PieroBorgatta/Laveggio-Printomatic/firmware/production-gateway/data/casklogicmark.png

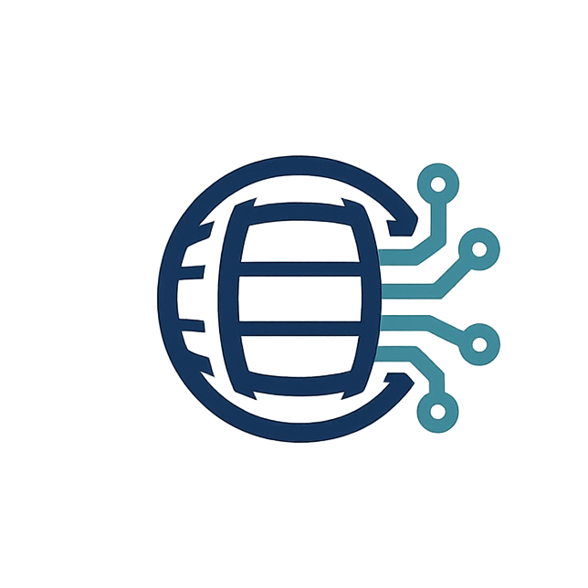
firmware/production-gateway/data/casklogicmark.png
