PieroBorgatta/Laveggio-Printomatic/firmware/production-gateway/include/OtaPublicKey.h

#pragma once

#include <Arduino.h>

// Chiave pubblica ECDSA-P256. La chiave privata non deve entrare nel repository.
// SHA-256 (SubjectPublicKeyInfo DER): c0b7adafcceb273d9163ec646b9b6864ba897b7cf9034c2e89df88110f6e895d
const uint8_t PUBLIC_KEY[] PROGMEM = {
  0x2d, 0x2d, 0x2d, 0x2d, 0x2d, 0x42, 0x45, 0x47, 0x49, 0x4e, 0x20, 0x50, 0x55, 0x42, 0x4c, 0x49,
  0x43, 0x20, 0x4b, 0x45, 0x59, 0x2d, 0x2d, 0x2d, 0x2d, 0x2d, 0x0d, 0x0a, 0x4d, 0x46, 0x6b, 0x77,
  0x45, 0x77, 0x59, 0x48, 0x4b, 0x6f, 0x5a, 0x49, 0x7a, 0x6a, 0x30, 0x43, 0x41, 0x51, 0x59, 0x49,
  0x4b, 0x6f, 0x5a, 0x49, 0x7a, 0x6a, 0x30, 0x44, 0x41, 0x51, 0x63, 0x44, 0x51, 0x67, 0x41, 0x45,
  0x7a, 0x4d, 0x30, 0x72, 0x68, 0x39, 0x41, 0x31, 0x44, 0x72, 0x57, 0x38, 0x44, 0x6a, 0x75, 0x44,
  0x50, 0x4d, 0x73, 0x73, 0x63, 0x30, 0x7a, 0x6f, 0x6b, 0x79, 0x5a, 0x62, 0x0d, 0x0a, 0x4a, 0x51,
  0x4d, 0x2f, 0x39, 0x2b, 0x4a, 0x52, 0x2f, 0x4f, 0x33, 0x41, 0x62, 0x6c, 0x38, 0x2b, 0x7a, 0x53,
  0x2b, 0x73, 0x61, 0x79, 0x43, 0x48, 0x2f, 0x66, 0x65, 0x2f, 0x75, 0x54, 0x42, 0x76, 0x4c, 0x74,
  0x69, 0x6c, 0x4a, 0x45, 0x46, 0x59, 0x34, 0x58, 0x6e, 0x53, 0x67, 0x59, 0x4d, 0x6f, 0x38, 0x4e,
  0x57, 0x6b, 0x30, 0x64, 0x4d, 0x4f, 0x48, 0x41, 0x3d, 0x3d, 0x0d, 0x0a, 0x2d, 0x2d, 0x2d, 0x2d,
  0x2d, 0x45, 0x4e, 0x44, 0x20, 0x50, 0x55, 0x42, 0x4c, 0x49, 0x43, 0x20, 0x4b, 0x45, 0x59, 0x2d,
  0x2d, 0x2d, 0x2d, 0x2d, 0x0d, 0x0a, 0x00,
};
const size_t PUBLIC_KEY_LEN = 183;
